M1S2/Garage_Door_Sensor/Sensor/Mechanical/Back_Lid_M3.stl

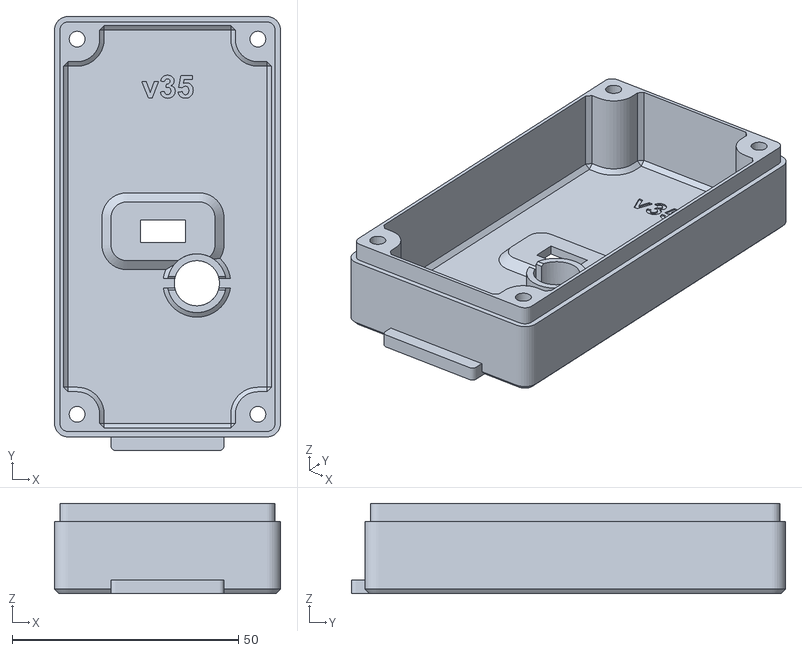
[picture p24: CAD file, 2024-05-25]
Sensor/Mechanical/Back_Lid_M3.stl
50.0 x 96.0 x 20.0
