M1S2/Garage_Door_Sensor/IndoorStation/Mechanical/Back_Lid_Text_M3.stl

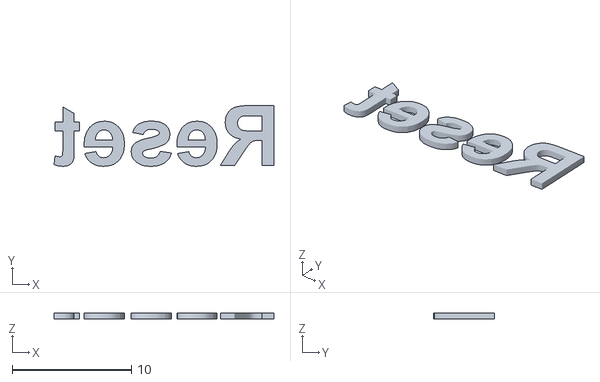
[picture p25: CAD file, 2024-05-17]
IndoorStation/Mechanical/Back_Lid_Text_M3.stl
18.4 x 5.08 x 0.5
