M1S2/Garage_Door_Sensor/Sensor/Mechanical/Front_Lid_M3.stl

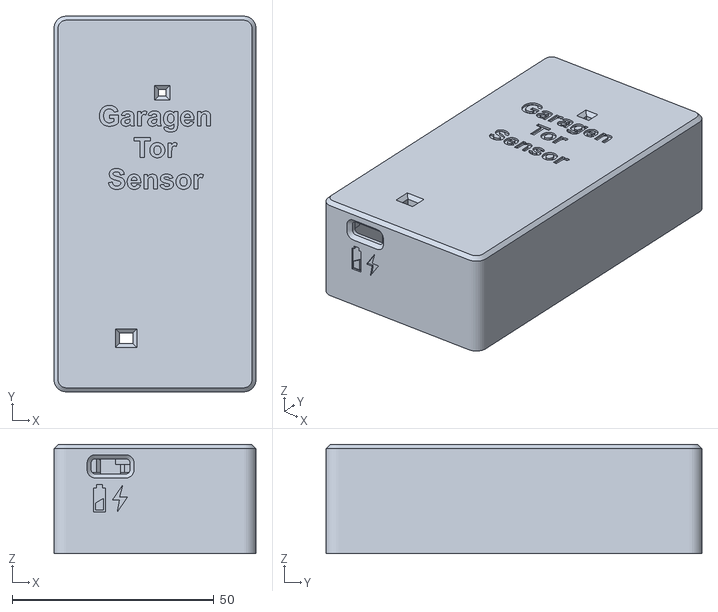
[picture p26: CAD file, 2024-05-25]
Sensor/Mechanical/Front_Lid_M3.stl
50.0 x 93.0 x 27.0
