M1S2/Garage_Door_Sensor/IndoorStation/Mechanical/Front_Lid_Text_M3.stl

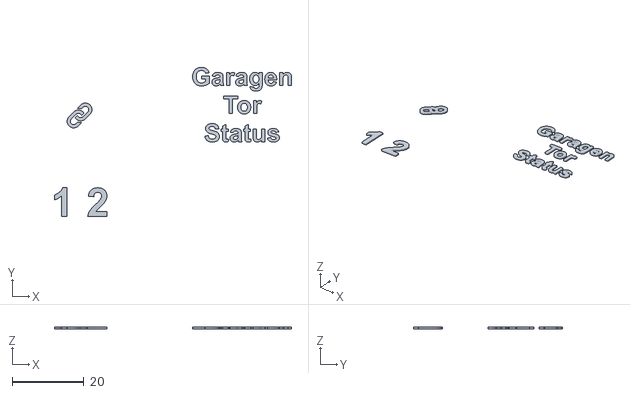
[picture p27: CAD file, 2024-05-17]
IndoorStation/Mechanical/Front_Lid_Text_M3.stl
65.9 x 41.5 x 0.5
