M1S2/Garage_Door_Sensor/Sensor/Mechanical/Magnet_Mount_Lid_M3.stl

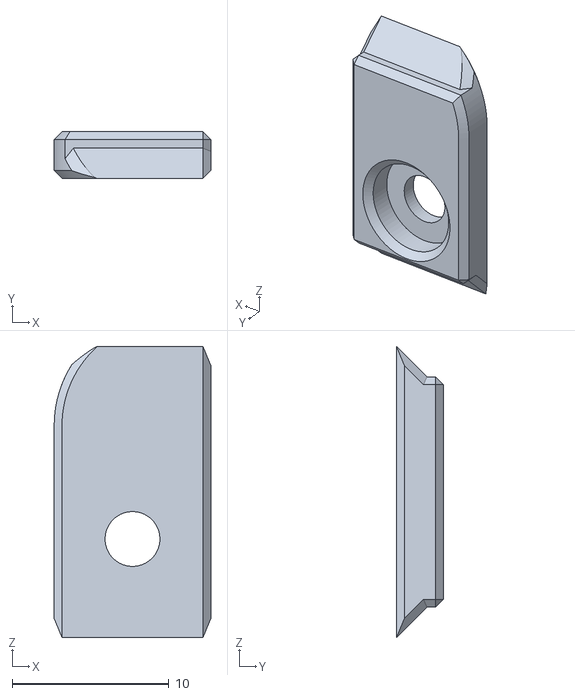
[picture p28: CAD file, 2024-05-17]
Sensor/Mechanical/Magnet_Mount_Lid_M3.stl
10.0 x 3.00 x 18.6
