M1S2/Garage_Door_Sensor/Sensor/Mechanical/Switch_Slider_Clamp_M3.stl

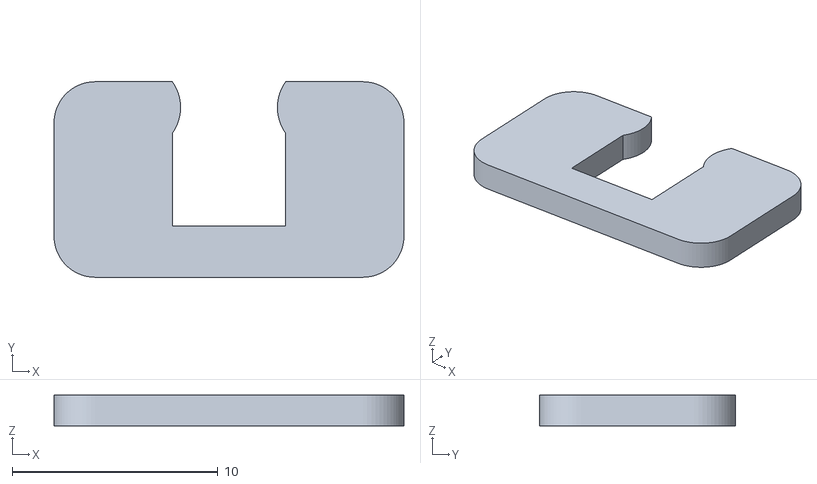
[picture p29: CAD file, 2024-05-17]
Sensor/Mechanical/Switch_Slider_Clamp_M3.stl
17.0 x 9.50 x 1.50
