M1S2/Garage_Door_Sensor/Sensor/Mechanical/LoadingModuleClamp_M3.stl

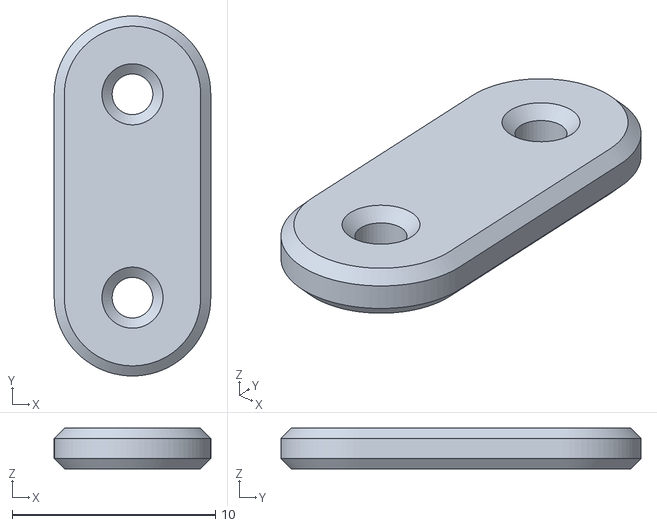
[picture p30: CAD file, 2024-05-17]
Sensor/Mechanical/LoadingModuleClamp_M3.stl
7.70 x 17.7 x 2.00
