M1S2/Garage_Door_Sensor/Sensor/Mechanical/Front_Lid_Text_M3.stl

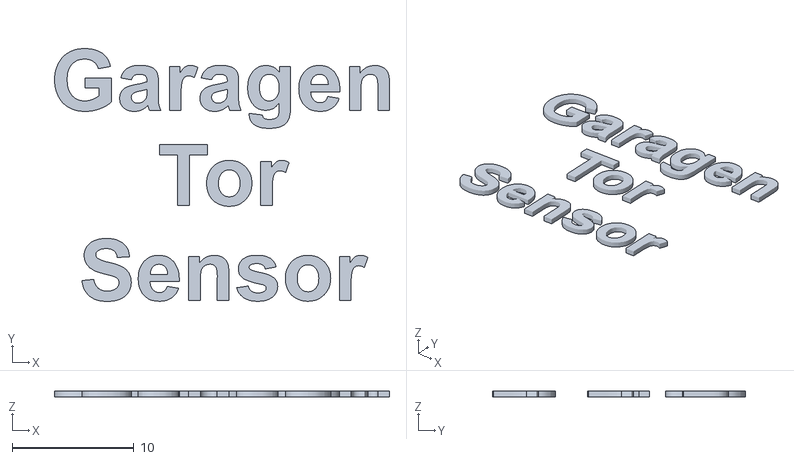
[picture p31: CAD file, 2024-05-17]
Sensor/Mechanical/Front_Lid_Text_M3.stl
27.5 x 20.8 x 0.5
