M1S2/Garage_Door_Sensor/Sensor/Mechanical/Back_Lid_Text_M3.stl

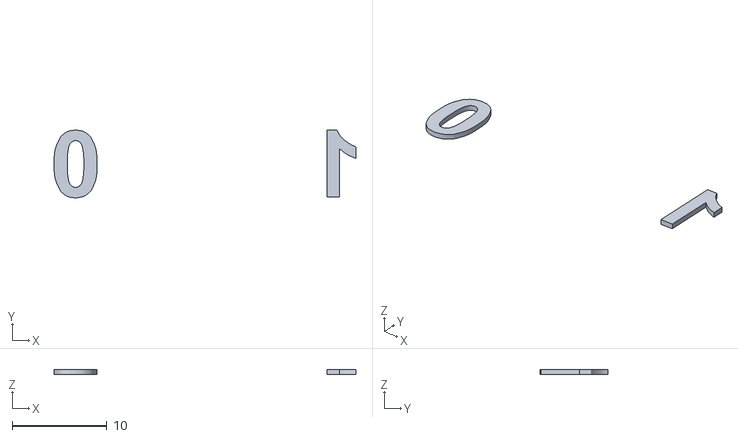
[picture p32: CAD file, 2024-05-17]
Sensor/Mechanical/Back_Lid_Text_M3.stl
31.8 x 7.15 x 0.5
