M1S2/Garage_Door_Sensor/Sensor/Mechanical/Magnet_Mount_M3.stl

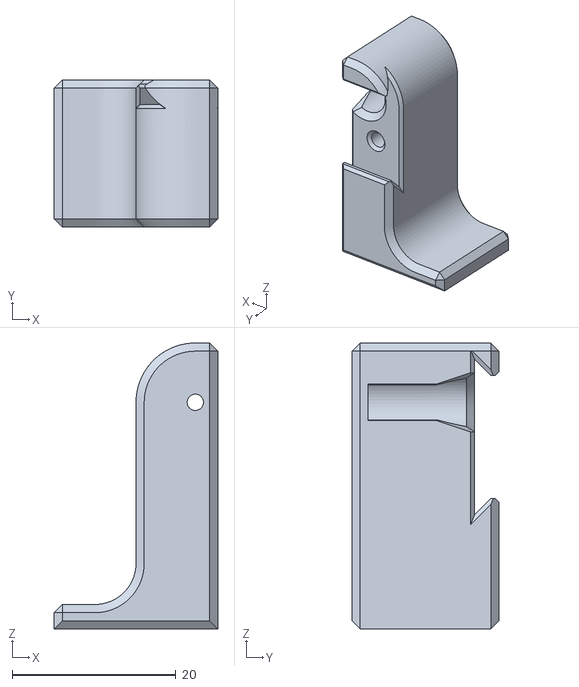
[picture p33: CAD file, 2024-05-17]
Sensor/Mechanical/Magnet_Mount_M3.stl
20.0 x 18.0 x 35.0
