M1S2/Garage_Door_Sensor/IndoorStation/Software/include/battery.h

#ifndef BATTERY_H
#define BATTERY_H

#include <Arduino.h>

/**
 * Convert the battery voltage in mV to an level in percent.
 * @param batteryVoltage_mV Measured voltage of the battery in mV.
 * @param numberFractionalDigits Number of fractional digits returned. E.g. numberFractionalDigits=2 --> return e.g. 3.14
 * @return Value between 0 and 100 indicating the battery level in percent. The return value uses the number of fractional digits given.
 */
float battery_voltageToPercent(uint16_t batteryVoltage_mV, uint8_t numberFractionalDigits = 2);

/**
 * Check if the battery is empty. It is regarded as empty, when the battery level in percent falls under threshold_percent
 * @param batteryVoltage_V Measured voltage of the battery in mV.
 * @param threshold_percent This is the threshold under which the battery is regarded as empty.
 * @return True, if the battery level is below threshold_percent; otherwise false.
 */
bool battery_isEmpty(uint16_t batteryVoltage_mV, uint8_t threshold_percent);

#endif
