M1S2/Garage_Door_Sensor/IndoorStation/Software/include/version.h

// This file includes the version information for the software components.
// The version below should match the one in the version.js file in the data directory!

#define GARAGE_DOOR_INDOOR_STATION_SW_VERSION     "NO_RELEASE"
