M1S2/Garage_Door_Sensor/Sensor/Software/include/version.h

#define SENSOR_SW_VERSION_MAJOR         0           // allowed range 0..15, use MAJOR=0 and MINOR=0 to indicate a development version
#define SENSOR_SW_VERSION_MINOR         0           // allowed range 0..15, use MAJOR=0 and MINOR=0 to indicate a development version
